rweather/vz200-restoration/schematics/RAM_ROM_Expansion/RAM_ROM_Expansion.kicad_pcb

## KiCad design schematics/RAM_ROM_Expansion/RAM_ROM_Expansion.kicad_pcb (2023-12-31)

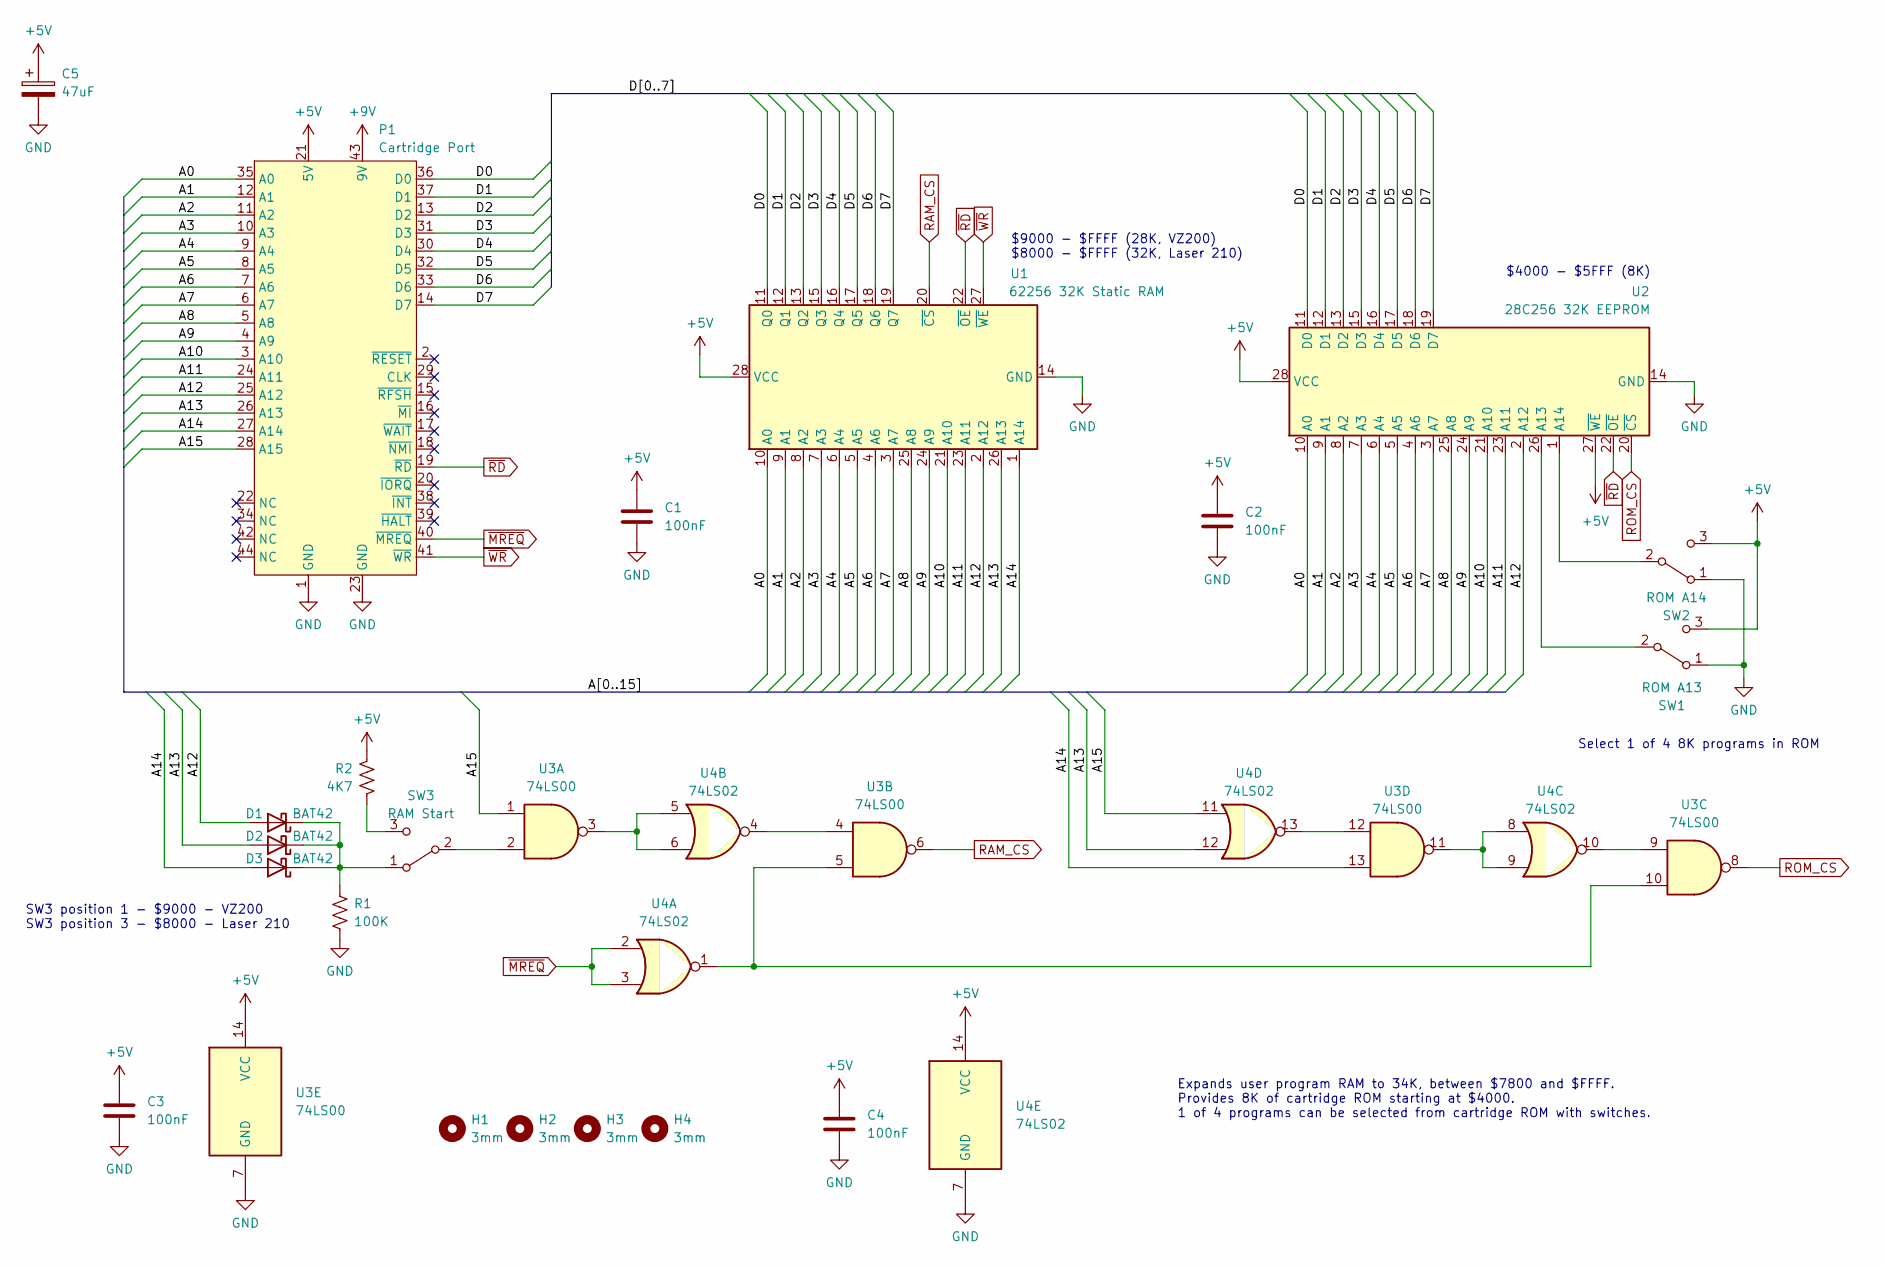
[picture p59: schematic RAM_ROM_Expansion.kicad_sch]

Parts:
C1, C2, C3, C4: 100nF; C_Disc_D5.0mm_W2.5mm_P5.00mm
C5: 47uF; CP_Radial_D6.3mm_P2.50mm
D1, D2, D3: BAT42; D_DO-35_SOD27_P7.62mm_Horizontal
H1, H2, H3, H4: 3mm; MountingHole_3mm
P1: Cartridge Port; VZ200_Cartridge_Port
R1: 100K; R_Axial_DIN0207_L6.3mm_D2.5mm_P7.62mm_Horizontal
R2: 4K7; R_Axial_DIN0207_L6.3mm_D2.5mm_P7.62mm_Horizontal
SW1: ROM A13; PinHeader_1x03_P2.54mm_Vertical
SW2: ROM A14; PinHeader_1x03_P2.54mm_Vertical
SW3: RAM Start; PinHeader_1x03_P2.54mm_Vertical
U1: 62256 32K Static RAM; DIP-28_W15.24mm_Socket
U2: 28C256 32K EEPROM; DIP-28_W15.24mm_Socket
U3: 74LS00; DIP-14_W7.62mm_Socket
U4: 74LS02; DIP-14_W7.62mm_Socket

Connections:
+5V: C1.1, C2.1, C3.1, C4.1, C5.1, P1.21 (5V), R2.1, SW1.3 (C), SW2.3 (C), U1.28 (VCC), U2.27 (~WE), U2.28 (VCC), U3.14 (VCC), U4.14 (VCC)
+9V: P1.43 (9V)
/A0: P1.35 (A0), U1.10 (A0), U2.10 (A0)
/A1: P1.12 (A1), U1.9 (A1), U2.9 (A1)
/A2: P1.11 (A2), U1.8 (A2), U2.8 (A2)
/A3: P1.10 (A3), U1.7 (A3), U2.7 (A3)
/A4: P1.9 (A4), U1.6 (A4), U2.6 (A4)
/A5: P1.8 (A5), U1.5 (A5), U2.5 (A5)
/A6: P1.7 (A6), U1.4 (A6), U2.4 (A6)
/A7: P1.6 (A7), U1.3 (A7), U2.3 (A7)
/A8: P1.5 (A8), U1.25 (A8), U2.25 (A8)
/A9: P1.4 (A9), U1.24 (A9), U2.24 (A9)
/A10: P1.3 (A10), U1.21 (A10), U2.21 (A10)
/A11: P1.24 (A11), U1.23 (A11), U2.23 (A11)
/A12: D1.2 (A), P1.25 (A12), U1.2 (A12), U2.2 (A12)
/A13: D2.2 (A), P1.26 (A13), U1.26 (A13), U4.12
/A14: D3.2 (A), P1.27 (A14), U1.1 (A14), U3.13
/A15: P1.28 (A15), U3.1, U4.11
/D0: P1.36 (D0), U1.11 (Q0), U2.11 (D0)
/D1: P1.37 (D1), U1.12 (Q1), U2.12 (D1)
/D2: P1.13 (D2), U1.13 (Q2), U2.13 (D2)
/D3: P1.31 (D3), U1.15 (Q3), U2.15 (D3)
/D4: P1.30 (D4), U1.16 (Q4), U2.16 (D4)
/D5: P1.32 (D5), U1.17 (Q5), U2.17 (D5)
/D6: P1.33 (D6), U1.18 (Q6), U2.18 (D6)
/D7: P1.14 (D7), U1.19 (Q7), U2.19 (D7)
GND: C1.2, C2.2, C3.2, C4.2, C5.2, P1.1 (GND), P1.23 (GND), R1.2, SW1.1 (A), SW2.1 (A), U1.14 (GND), U2.14 (GND), U3.7 (GND), U4.7 (GND)
unnamed: D1.1 (K), D2.1 (K), D3.1 (K), R1.1, SW3.1 (A)
unnamed: SW1.2 (B), U2.26 (A13)
unnamed: SW2.2 (B), U2.1 (A14)
unnamed: SW3.2 (B), U3.2
unnamed: R2.2, SW3.3 (C)
unnamed: U3.3, U4.5, U4.6
unnamed: U3.4, U4.4
unnamed: U3.9, U4.10
unnamed: U3.5, U3.10, U4.1
unnamed: U3.11, U4.8, U4.9
unnamed: U3.12, U4.13
RAM_CS: U1.20 (~CS), U3.6
ROM_CS: U2.20 (~CS), U3.8
~MREQ: P1.40 (~MREQ), U4.2, U4.3
~RD: P1.19 (~RD), U1.22 (~OE), U2.22 (~OE)
~WR: P1.41 (~WR), U1.27 (~WE)

Notes on the sheet:
Expands user program RAM to 34K, between $7800 and $FFFF. Provides 8K of cartridge ROM starting at $4000. 1 of 4 programs can be selected from cartridge ROM with switches.
Select 1 of 4 8K programs in ROM
$4000 - $5FFF (8K)
SW3 position 1 - $9000 - VZ200 SW3 position 3 - $8000 - Laser 210
$9000 - $FFFF (28K, VZ200) $8000 - $FFFF (32K, Laser 210)

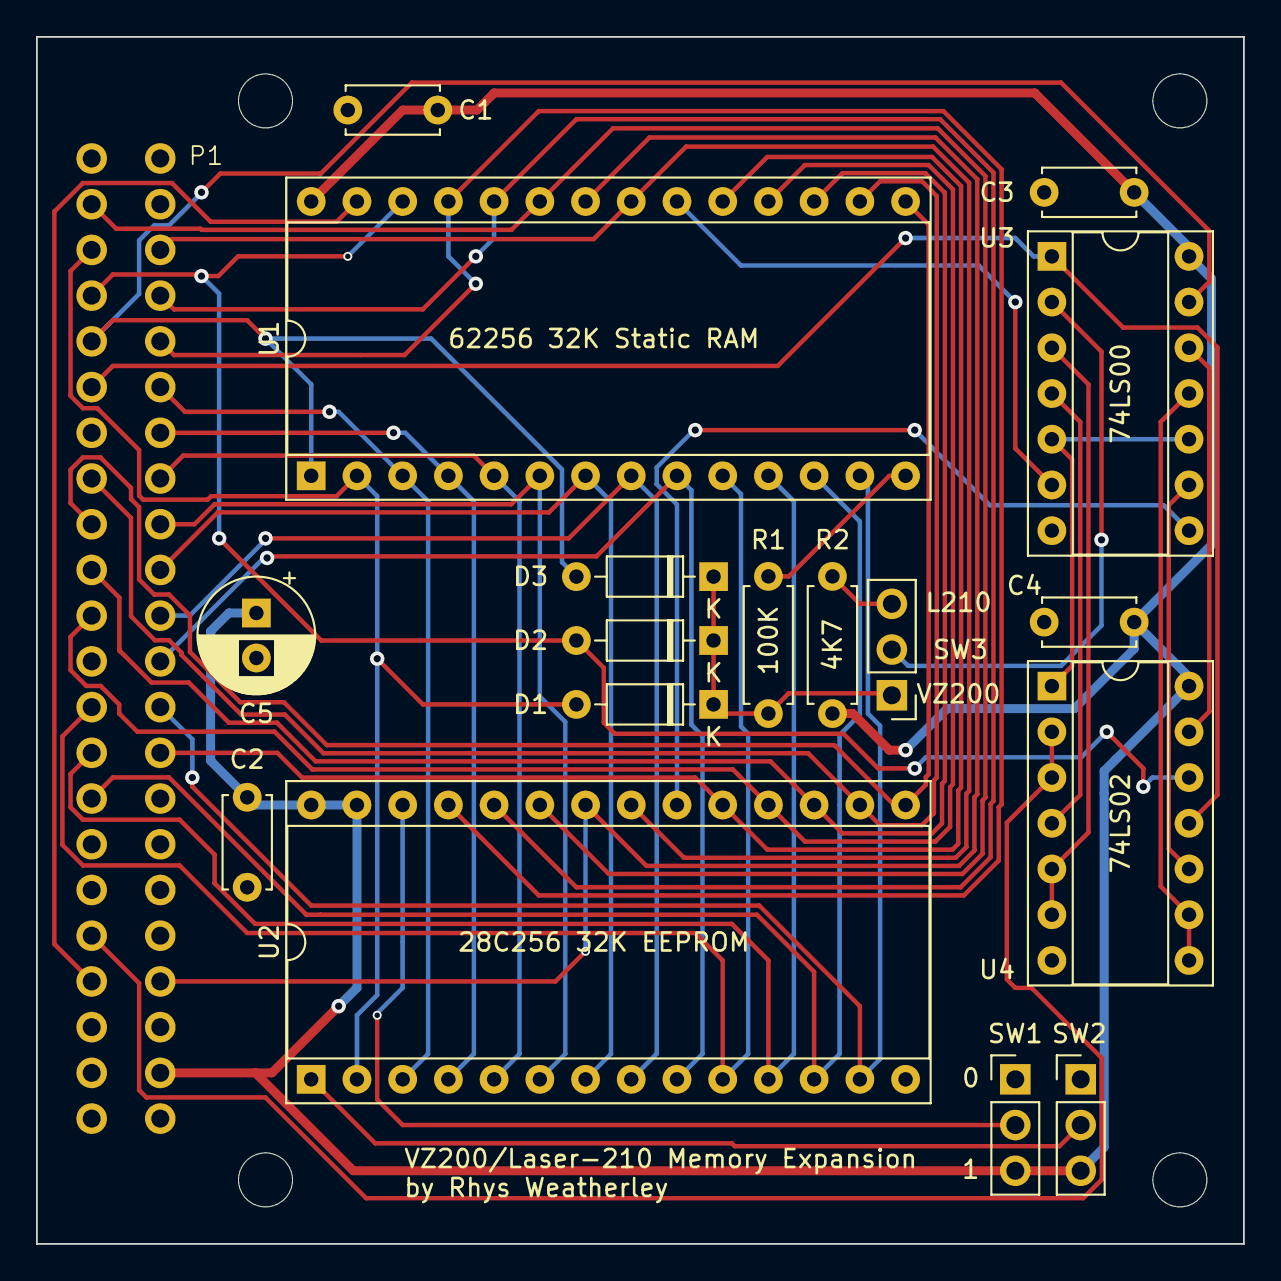
[picture p60: board RAM_ROM_Expansion.kicad_pcb from above]

Board: 2 copper layers, 67.1 x 67.1 mm, 22 parts (0 on the bottom side), 42 nets.
